kellerkindt/bluepill_sensor/src/bme280.rs

//! A platform agnostic Rust driver for the Bosch BME280 and BMP280, based on the
//! [`embedded-hal`](https://github.com/japaric/embedded-hal) traits.
//!
//! ## The Device
//!
//! The [Bosch BME280](https://www.bosch-sensortec.com/bst/products/all_products/bme280)
//! is a highly accurate sensor for atmospheric temperature, pressure, and
//! relative humidity.
//!
//! The [Bosch BMP280](https://www.bosch-sensortec.com/bst/products/all_products/bmp280)
//! is a highly accurate sensor for atmospheric temperature, and pressure.
//!
//! The device has I²C and SPI interfaces (SPI is not currently supported).
//!
//! ## Usage
//!
//! ```no_run
//! extern crate linux_embedded_hal as hal;
//! extern crate bme280;
//!
//! use hal::{Delay, I2cdev};
//! use bme280::BME280;
//!
//! // using Linux I2C Bus #1 in this example
//! let i2c_bus = I2cdev::new("/dev/i2c-1").unwrap();
//!
//! // initialize the BME280 using the primary I2C address 0x77
//! let mut bme280 = BME280::new_primary(i2c_bus, Delay);
//!
//! // or, initialize the BME280 using the secondary I2C address 0x78
//! // let mut bme280 = BME280::new_secondary(i2c_bus, Delay);
//!
//! // or, initialize the BME280 using a custom I2C address
//! // let bme280_i2c_addr = 0x88;
//! // let mut bme280 = BME280::new(i2c_bus, bme280_i2c_addr, Delay);
//!
//! // initialize the sensor
//! bme280.init().unwrap();
//!
//! // measure temperature, pressure, and humidity
//! let measurements = bme280.measure().unwrap();
//!
//! println!("Relative Humidity = {}%", measurements.humidity);
//! println!("Temperature = {} deg C", measurements.temperature);
//! println!("Pressure = {} pascals", measurements.pressure);
//! ```

extern crate embedded_hal;
use nb::Error as NbError;

use bme280::I2cError::I2c;
use core::marker::PhantomData;
use embedded_hal::blocking::delay::DelayMs;
use embedded_hal::blocking::i2c::{Read, Write, WriteRead};
use stm32f1xx_hal::delay::Delay;
use stm32f1xx_hal::i2c::Error as I2cErrorHal;

const BME280_I2C_ADDR_PRIMARY: u8 = 0x76;
const BME280_I2C_ADDR_SECONDARY: u8 = 0x77;

const BME280_PWR_CTRL_ADDR: u8 = 0xF4;
const BME280_CTRL_HUM_ADDR: u8 = 0xF2;
const BME280_CTRL_MEAS_ADDR: u8 = 0xF4;
const BME280_CONFIG_ADDR: u8 = 0xF5;

const BME280_RESET_ADDR: u8 = 0xE0;
const BME280_SOFT_RESET_CMD: u8 = 0xB6;

const BME280_CHIP_ID: u8 = 0x60;
const BMP280_CHIP_ID: u8 = 0x58;
const BME280_CHIP_ID_ADDR: u8 = 0xD0;

const BME280_DATA_ADDR: u8 = 0xF7;
const BME280_P_T_H_DATA_LEN: usize = 8;

const BME280_P_T_CALIB_DATA_ADDR: u8 = 0x88;
const BME280_P_T_CALIB_DATA_LEN: usize = 26;

const BME280_H_CALIB_DATA_ADDR: u8 = 0xE1;
const BME280_H_CALIB_DATA_LEN: usize = 7;

const BME280_TEMP_MIN: f32 = -40.0;
const BME280_TEMP_MAX: f32 = 85.0;

const BME280_PRESSURE_MIN: f32 = 30000.0;
const BME280_PRESSURE_MAX: f32 = 110000.0;

const BME280_HUMIDITY_MIN: f32 = 0.0;
const BME280_HUMIDITY_MAX: f32 = 100.0;

const BME280_SLEEP_MODE: u8 = 0x00;
const BME280_FORCED_MODE: u8 = 0x01;
const BME280_NORMAL_MODE: u8 = 0x03;

const BME280_SENSOR_MODE_MSK: u8 = 0x03;

const BME280_CTRL_HUM_MSK: u8 = 0x07;

const BME280_CTRL_PRESS_MSK: u8 = 0x1C;
const BME280_CTRL_PRESS_POS: u8 = 0x02;

const BME280_CTRL_TEMP_MSK: u8 = 0xE0;
const BME280_CTRL_TEMP_POS: u8 = 0x05;

const BME280_FILTER_MSK: u8 = 0x1C;
const BME280_FILTER_POS: u8 = 0x02;
const BME280_FILTER_COEFF_16: u8 = 0x04;

const BME280_OVERSAMPLING_1X: u8 = 0x01;
const BME280_OVERSAMPLING_2X: u8 = 0x02;
const BME280_OVERSAMPLING_16X: u8 = 0x05;

macro_rules! concat_bytes {
    ($msb:expr, $lsb:expr) => {
        (($msb as u16) << 8) | ($lsb as u16)
    };
}

macro_rules! set_bits {
    ($reg_data:expr, $mask:expr, $pos:expr, $data:expr) => {
        ($reg_data & !$mask) | (($data << $pos) & $mask)
    };
}

/// BME280 errors
pub enum I2cError<E> {
    /// Failed to compensate a raw measurement
    CompensationFailed,
    /// I²C bus error
    I2c(E),
    /// Failed to parse sensor data
    InvalidData,
    /// No calibration data is available (probably forgot to call or check BME280::init for failure)
    NoCalibrationData,
    /// Chip ID doesn't match expected value
    UnsupportedChip,
}

impl From<I2cErrorHal> for I2cError<I2cErrorHal> {
    fn from(i2c: I2cErrorHal) -> Self {
        I2cError::I2c(i2c)
    }
}

/// BME280 operating mode
#[derive(Copy, Clone)]
pub enum SensorMode {
    /// Sleep mode
    Sleep,
    /// Forced mode
    Forced,
    /// Normal mode
    Normal,
}

struct CalibrationData {
    dig_t1: u16,
    dig_t2: i16,
    dig_t3: i16,
    dig_p1: u16,
    dig_p2: i16,
    dig_p3: i16,
    dig_p4: i16,
    dig_p5: i16,
    dig_p6: i16,
    dig_p7: i16,
    dig_p8: i16,
    dig_p9: i16,
    dig_h1: u8,
    dig_h2: i16,
    dig_h3: u8,
    dig_h4: i16,
    dig_h5: i16,
    dig_h6: i8,
    t_fine: i32,
}

/// Measurement data
pub struct Measurements<E> {
    /// temperature in degrees celsius
    pub temperature: f32,
    /// pressure in pascals
    pub pressure: f32,
    /// percent relative humidity (`0` with BMP280)
    pub humidity: f32,
    _e: PhantomData<E>,
}

impl<E> Measurements<I2cError<E>> {
    fn parse(
        data: [u8; BME280_P_T_H_DATA_LEN],
        calibration: &mut CalibrationData,
    ) -> Result<Self, I2cError<E>> {
        let data_msb: u32 = (data[0] as u32) << 12;
        let data_lsb: u32 = (data[1] as u32) << 4;
        let data_xlsb: u32 = (data[2] as u32) >> 4;
        let pressure = data_msb | data_lsb | data_xlsb;

        let data_msb: u32 = (data[3] as u32) << 12;
        let data_lsb: u32 = (data[4] as u32) << 4;
        let data_xlsb: u32 = (data[5] as u32) >> 4;
        let temperature = data_msb | data_lsb | data_xlsb;

        let data_msb: u32 = (data[6] as u32) << 8;
        let data_lsb: u32 = data[7] as u32;
        let humidity = data_msb | data_lsb;

        let temperature = Measurements::compensate_temperature(temperature, calibration)?;
        let pressure = Measurements::compensate_pressure(pressure, calibration)?;
        let humidity = Measurements::compensate_humidity(humidity, calibration)?;

        Ok(Measurements {
            temperature,
            pressure,
            humidity,
            _e: PhantomData,
        })
    }

    fn compensate_temperature(
        uncompensated: u32,
        calibration: &mut CalibrationData,
    ) -> Result<f32, I2cError<E>> {
        let var1: f32 = uncompensated as f32 / 16384.0 - calibration.dig_t1 as f32 / 1024.0;
        let var1 = var1 * calibration.dig_t2 as f32;
        let var2 = uncompensated as f32 / 131072.0 - calibration.dig_t1 as f32 / 8192.0;
        let var2 = var2 * var2 * calibration.dig_t3 as f32;

        calibration.t_fine = (var1 + var2) as i32;

        let temperature = (var1 + var2) / 5120.0;
        let temperature = if temperature < BME280_TEMP_MIN {
            BME280_TEMP_MIN
        } else if temperature > BME280_TEMP_MAX {
            BME280_TEMP_MAX
        } else {
            temperature
        };
        Ok(temperature)
    }

    fn compensate_pressure(
        uncompensated: u32,
        calibration: &mut CalibrationData,
    ) -> Result<f32, I2cError<E>> {
        let var1: f32 = calibration.t_fine as f32 / 2.0 - 64000.0;
        let var2: f32 = var1 * var1 * calibration.dig_p6 as f32 / 32768.0;
        let var2: f32 = var2 + var1 * calibration.dig_p5 as f32 * 2.0;
        let var2: f32 = var2 / 4.0 + calibration.dig_p4 as f32 * 65536.0;
        let var3: f32 = calibration.dig_p3 as f32 * var1 * var1 / 524288.0;
        let var1: f32 = (var3 + calibration.dig_p2 as f32 * var1) / 524288.0;
        let var1: f32 = (1.0 + var1 / 32768.0) * calibration.dig_p1 as f32;

        let pressure = if var1 > 0.0 {
            let pressure: f32 = 1048576.0 - uncompensated as f32;
            let pressure: f32 = (pressure - (var2 / 4096.0)) * 6250.0 / var1;
            let var1: f32 = calibration.dig_p9 as f32 * pressure * pressure / 2147483648.0;
            let var2: f32 = pressure * calibration.dig_p8 as f32 / 32768.0;
            let pressure: f32 = pressure + (var1 + var2 + calibration.dig_p7 as f32) / 16.0;
            if pressure < BME280_PRESSURE_MIN {
                BME280_PRESSURE_MIN
            } else if pressure > BME280_PRESSURE_MAX {
                BME280_PRESSURE_MAX
            } else {
                pressure
            }
        } else {
            return Err(I2cError::InvalidData);
        };
        Ok(pressure)
    }

    fn compensate_humidity(
        uncompensated: u32,
        calibration: &mut CalibrationData,
    ) -> Result<f32, I2cError<E>> {
        let var1: f32 = calibration.t_fine as f32 - 76800.0;
        let var2: f32 =
            calibration.dig_h4 as f32 * 64.0 + (calibration.dig_h5 as f32 / 16384.0) * var1;
        let var3: f32 = uncompensated as f32 - var2;
        let var4: f32 = calibration.dig_h2 as f32 / 65536.0;
        let var5: f32 = 1.0 + (calibration.dig_h3 as f32 / 67108864.0) * var1;
        let var6: f32 = 1.0 + (calibration.dig_h6 as f32 / 67108864.0) * var1 * var5;
        let var6: f32 = var3 * var4 * (var5 * var6);

        let humidity: f32 = var6 * (1.0 - calibration.dig_h1 as f32 * var6 / 524288.0);
        let humidity = if humidity < BME280_HUMIDITY_MIN {
            BME280_HUMIDITY_MIN
        } else if humidity > BME280_HUMIDITY_MAX {
            BME280_HUMIDITY_MAX
        } else {
            humidity
        };
        Ok(humidity)
    }
}

/// Representation of a BME280
pub struct BME280<'a> {
    /// concrete I²C device implementation
    i2c: &'a mut WriteRead<Error = NbError<I2cErrorHal>>,
    /// I²C device address
    address: u8,
    /// concrete Delay implementation
    delay: &'a mut Delay,
    /// calibration data
    calibration: Option<CalibrationData>,
}

impl<'a> BME280<'a> {
    /// Create a new BME280 struct using the primary I²C address `0x76`
    pub fn new_primary(
        i2c: &'a mut WriteRead<Error = NbError<I2cErrorHal>>,
        delay: &'a mut Delay,
    ) -> Self {
        Self::new(i2c, BME280_I2C_ADDR_PRIMARY, delay)
    }

    /// Create a new BME280 struct using the secondary I²C address `0x77`
    pub fn new_secondary(
        i2c: &'a mut WriteRead<Error = NbError<I2cErrorHal>>,
        delay: &'a mut Delay,
    ) -> Self {
        Self::new(i2c, BME280_I2C_ADDR_SECONDARY, delay)
    }

    /// Create a new BME280 struct using a custom I²C address
    pub fn new(
        i2c: &'a mut WriteRead<Error = NbError<I2cErrorHal>>,
        address: u8,
        delay: &'a mut Delay,
    ) -> Self {
        BME280 {
            i2c,
            address,
            delay,
            calibration: None,
        }
    }

    /// Initializes the BME280
    pub fn init(&mut self) -> Result<(), I2cError<I2cErrorHal>> {
        self.verify_chip_id()?;
        self.soft_reset()?;
        self.calibrate()?;
        self.configure()
    }

    fn verify_chip_id(&mut self) -> Result<(), I2cError<I2cErrorHal>> {
        let chip_id = self.read_register(BME280_CHIP_ID_ADDR)?;
        if chip_id == BME280_CHIP_ID || chip_id == BMP280_CHIP_ID {
            Ok(())
        } else {
            Err(I2cError::UnsupportedChip)
        }
    }

    fn soft_reset(&mut self) -> Result<(), I2cError<I2cErrorHal>> {
        self.write_register(BME280_RESET_ADDR, BME280_SOFT_RESET_CMD)?;
        self.delay.delay_ms(2_u8); // startup time is 2ms
        Ok(())
    }

    fn calibrate(&mut self) -> Result<(), I2cError<I2cErrorHal>> {
        let pt_calib_data = self.read_pt_calib_data(BME280_P_T_CALIB_DATA_ADDR)?;
        let h_calib_data = self.read_h_calib_data(BME280_H_CALIB_DATA_ADDR)?;
        self.calibration = Some(parse_calib_data(&pt_calib_data, &h_calib_data));
        Ok(())
    }

    fn configure(&mut self) -> Result<(), I2cError<I2cErrorHal>> {
        match self.mode()? {
            SensorMode::Sleep => {}
            _ => self.soft_reset()?,
        };

        self.write_register(
            BME280_CTRL_HUM_ADDR,
            BME280_OVERSAMPLING_1X & BME280_CTRL_HUM_MSK,
        )?;
        let ctrl_meas = self.read_register(BME280_CTRL_MEAS_ADDR)?;
        self.write_register(BME280_CTRL_MEAS_ADDR, ctrl_meas)?;

        let data = self.read_register(BME280_CTRL_MEAS_ADDR)?;
        let data = set_bits!(
            data,
            BME280_CTRL_PRESS_MSK,
            BME280_CTRL_PRESS_POS,
            BME280_OVERSAMPLING_16X
        );
        let data = set_bits!(
            data,
            BME280_CTRL_TEMP_MSK,
            BME280_CTRL_TEMP_POS,
            BME280_OVERSAMPLING_2X
        );
        self.write_register(BME280_CTRL_MEAS_ADDR, data)?;

        let data = self.read_register(BME280_CONFIG_ADDR)?;
        let data = set_bits!(
            data,
            BME280_FILTER_MSK,
            BME280_FILTER_POS,
            BME280_FILTER_COEFF_16
        );
        self.write_register(BME280_CONFIG_ADDR, data)
    }

    fn mode(&mut self) -> Result<SensorMode, I2cError<I2cErrorHal>> {
        let mut data: [u8; 1] = [0];
        block!(self
            .i2c
            .write_read(self.address, &[BME280_PWR_CTRL_ADDR], &mut data))
        .map_err(I2cError::I2c)?;
        match data[0] & BME280_SENSOR_MODE_MSK {
            BME280_SLEEP_MODE => Ok(SensorMode::Sleep),
            BME280_FORCED_MODE => Ok(SensorMode::Forced),
            BME280_NORMAL_MODE => Ok(SensorMode::Normal),
            _ => Err(I2cError::InvalidData),
        }
    }

    fn forced(&mut self) -> Result<(), I2cError<I2cErrorHal>> {
        self.set_mode(BME280_FORCED_MODE)
    }

    fn set_mode(&mut self, mode: u8) -> Result<(), I2cError<I2cErrorHal>> {
        match self.mode()? {
            SensorMode::Sleep => {}
            _ => self.soft_reset()?,
        };
        let data = self.read_register(BME280_PWR_CTRL_ADDR)?;
        let data = set_bits!(data, BME280_SENSOR_MODE_MSK, 0, mode);
        self.write_register(BME280_PWR_CTRL_ADDR, data)
    }

    /// Captures and processes sensor data for temperature, pressure, and humidity
    pub fn measure(
        &mut self,
    ) -> Result<Measurements<I2cError<I2cErrorHal>>, I2cError<I2cErrorHal>> {
        self.forced()?;
        self.delay.delay_ms(40_u8); // await measurement
        let measurements = self.read_data(BME280_DATA_ADDR)?;
        match self.calibration.as_mut() {
            Some(calibration) => {
                let measurements = Measurements::parse(measurements, &mut *calibration)?;
                Ok(measurements)
            }
            None => Err(I2cError::NoCalibrationData),
        }
    }

    fn read_register(&mut self, register: u8) -> Result<u8, I2cError<I2cErrorHal>> {
        let mut data: [u8; 1] = [0];
        block!(self.i2c.write_read(self.address, &[register], &mut data)).map_err(I2cError::I2c)?;
        Ok(data[0])
    }

    fn read_data(
        &mut self,
        register: u8,
    ) -> Result<[u8; BME280_P_T_H_DATA_LEN], I2cError<I2cErrorHal>> {
        let mut data: [u8; BME280_P_T_H_DATA_LEN] = [0; BME280_P_T_H_DATA_LEN];
        block!(self.i2c.write_read(self.address, &[register], &mut data)).map_err(I2cError::I2c)?;
        Ok(data)
    }

    fn read_pt_calib_data(
        &mut self,
        register: u8,
    ) -> Result<[u8; BME280_P_T_CALIB_DATA_LEN], I2cError<I2cErrorHal>> {
        let mut data: [u8; BME280_P_T_CALIB_DATA_LEN] = [0; BME280_P_T_CALIB_DATA_LEN];
        block!(self.i2c.write_read(self.address, &[register], &mut data))?;
        Ok(data)
    }

    fn read_h_calib_data(
        &mut self,
        register: u8,
    ) -> Result<[u8; BME280_H_CALIB_DATA_LEN], I2cError<I2cErrorHal>> {
        let mut data: [u8; BME280_H_CALIB_DATA_LEN] = [0; BME280_H_CALIB_DATA_LEN];
        block!(self.i2c.write_read(self.address, &[register], &mut data))?;
        Ok(data)
    }

    fn write_register(&mut self, register: u8, payload: u8) -> Result<(), I2cError<I2cErrorHal>> {
        block!(self
            .i2c
            .write_read(self.address, &[register, payload], &mut []))?;
        Ok(())
    }
}

fn parse_calib_data(
    pt_data: &[u8; BME280_P_T_CALIB_DATA_LEN],
    h_data: &[u8; BME280_H_CALIB_DATA_LEN],
) -> CalibrationData {
    let dig_t1 = concat_bytes!(pt_data[1], pt_data[0]);
    let dig_t2 = concat_bytes!(pt_data[3], pt_data[2]) as i16;
    let dig_t3 = concat_bytes!(pt_data[5], pt_data[4]) as i16;
    let dig_p1 = concat_bytes!(pt_data[7], pt_data[6]);
    let dig_p2 = concat_bytes!(pt_data[9], pt_data[8]) as i16;
    let dig_p3 = concat_bytes!(pt_data[11], pt_data[10]) as i16;
    let dig_p4 = concat_bytes!(pt_data[13], pt_data[12]) as i16;
    let dig_p5 = concat_bytes!(pt_data[15], pt_data[14]) as i16;
    let dig_p6 = concat_bytes!(pt_data[17], pt_data[16]) as i16;
    let dig_p7 = concat_bytes!(pt_data[19], pt_data[18]) as i16;
    let dig_p8 = concat_bytes!(pt_data[21], pt_data[20]) as i16;
    let dig_p9 = concat_bytes!(pt_data[23], pt_data[22]) as i16;
    let dig_h1 = pt_data[25];
    let dig_h2 = concat_bytes!(h_data[1], h_data[0]) as i16;
    let dig_h3 = h_data[2];
    let dig_h4 = (h_data[3] as i16 * 16) | ((h_data[4] as i16) & 0x0F);
    let dig_h5 = (h_data[5] as i16 * 16) | ((h_data[4] as i16) >> 4);
    let dig_h6 = h_data[6] as i8;

    CalibrationData {
        dig_t1,
        dig_t2,
        dig_t3,
        dig_p1,
        dig_p2,
        dig_p3,
        dig_p4,
        dig_p5,
        dig_p6,
        dig_p7,
        dig_p8,
        dig_p9,
        dig_h1,
        dig_h2,
        dig_h3,
        dig_h4,
        dig_h5,
        dig_h6,
        t_fine: 0,
    }
}
